impatrq/visiondrive/Cableado_Frenos_Luces/Cableado parte 1 vehiculo1.jpg

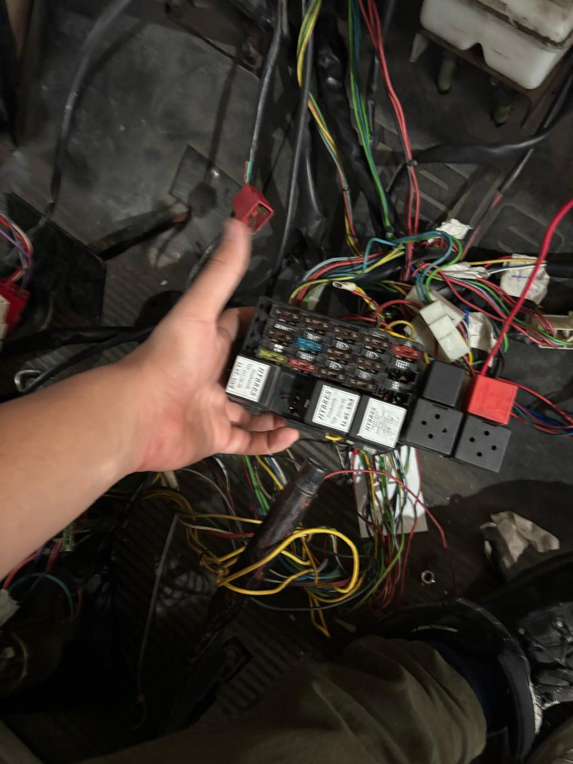
Cableado_Frenos_Luces/Cableado parte 1 vehiculo1.jpg
