impatrq/visiondrive/Cableado_Frenos_Luces/cableado parte 2 vehiculo 1.jpg

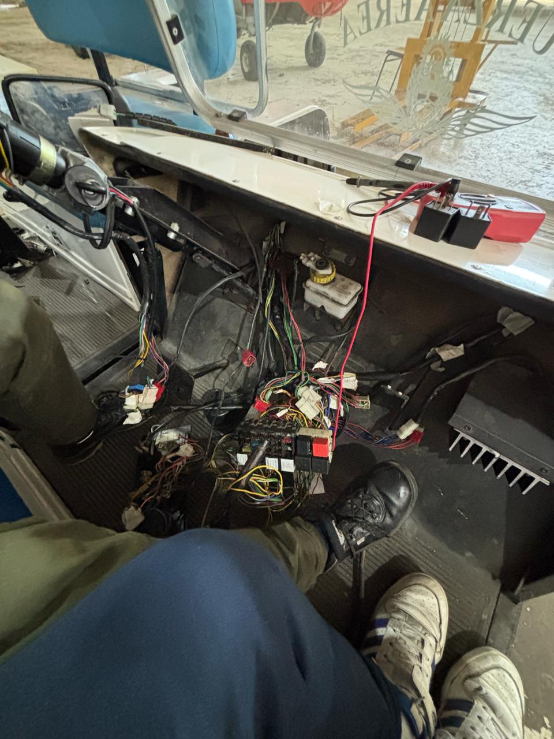
Cableado_Frenos_Luces/cableado parte 2 vehiculo 1.jpg
