impatrq/visiondrive/Carros Melex/Armado/Opticas/Imagen de WhatsApp 2024-11-14 a las 22.56.18_2eb6550c.jpg

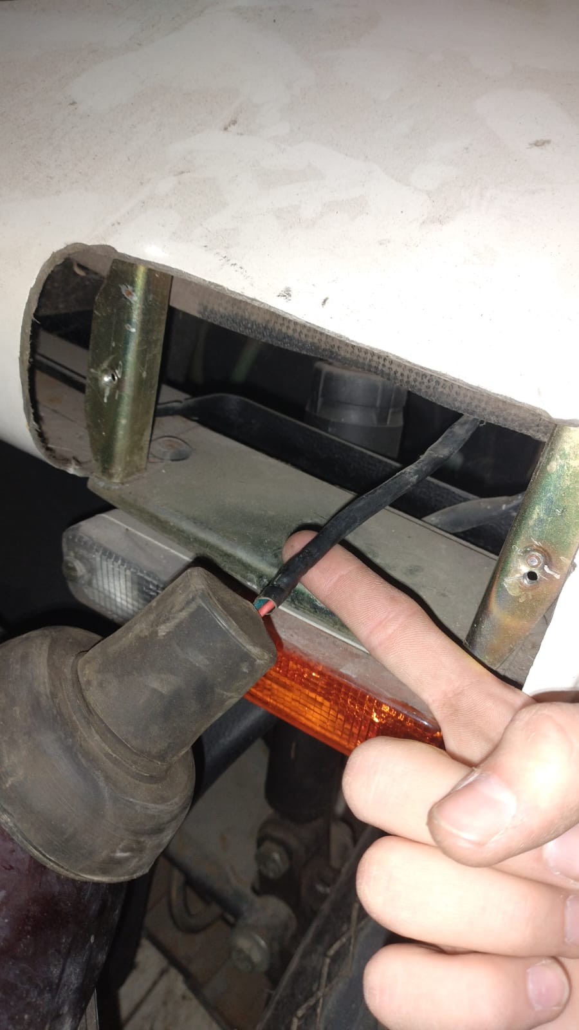
Carros Melex/Armado/Opticas/Imagen de WhatsApp 2024-11-14 a las 22.56.18_2eb6550c.jpg
