impatrq/visiondrive/Documentación/Diagramas de bloques/diagrama de bloques actualizado.png

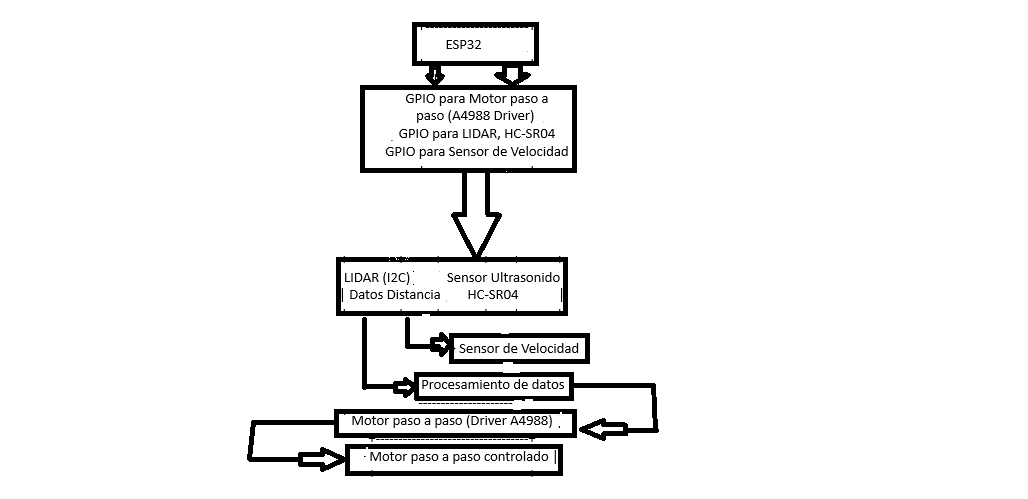
Documentación/Diagramas de bloques/diagrama de bloques actualizado.png
