impatrq/visiondrive/Documentación/Diagramas de bloques/diagrama de bloques.png

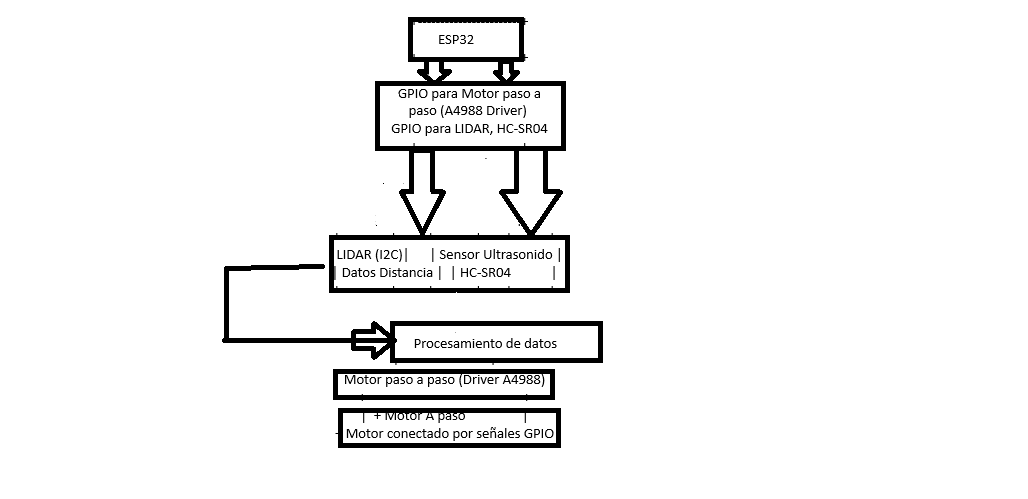
Documentación/Diagramas de bloques/diagrama de bloques.png
