impatrq/visiondrive/Impresiones 3D/Diseños de piezas 3d/diseño de segunda pieza 3d .jpg

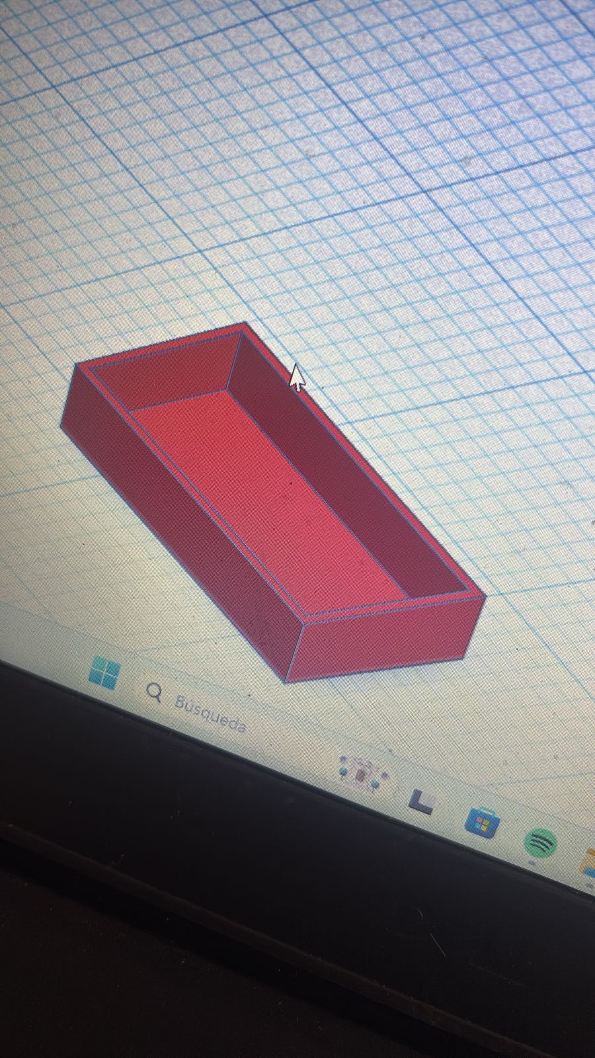
Impresiones 3D/Diseños de piezas 3d/diseño de segunda pieza 3d .jpg
