impatrq/visiondrive/Impresiones 3D/Piezas 3D/16E25E6C-24CF-4ABC-BED1-2C66113891F4.jpeg

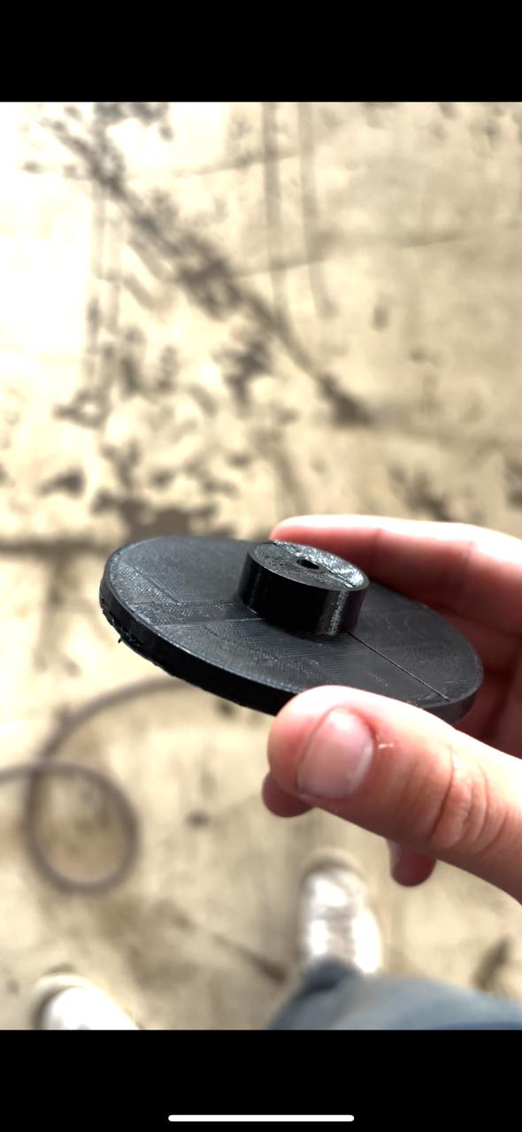
Impresiones 3D/Piezas 3D/16E25E6C-24CF-4ABC-BED1-2C66113891F4.jpeg
