impatrq/visiondrive/Impresiones 3D/Piezas 3D/265E03B3-B8B3-4103-B149-0D53786FD9E9_1_105_c.jpeg

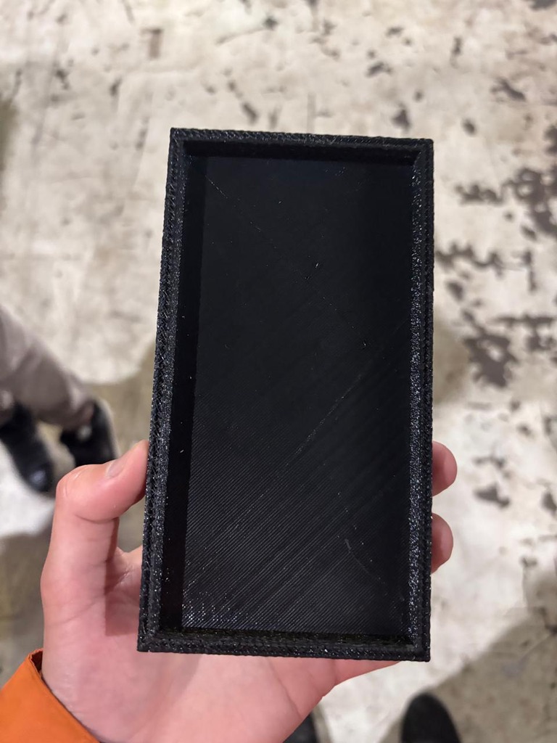
Impresiones 3D/Piezas 3D/265E03B3-B8B3-4103-B149-0D53786FD9E9_1_105_c.jpeg
