impatrq/visiondrive/mano de obra freno/20241107_143116.jpg

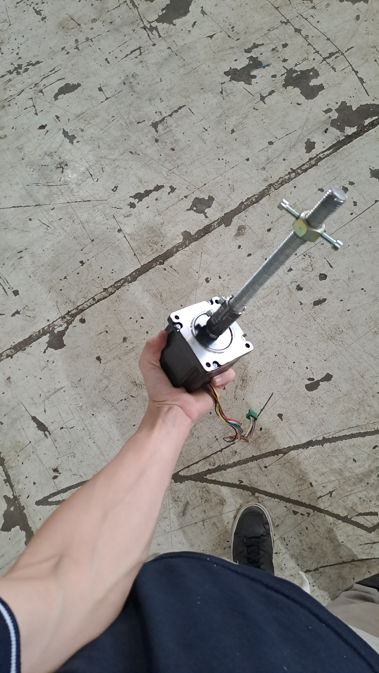
mano de obra freno/20241107_143116.jpg
