impatrq/visiondrive/mano de obra freno/20241107_165553.jpg

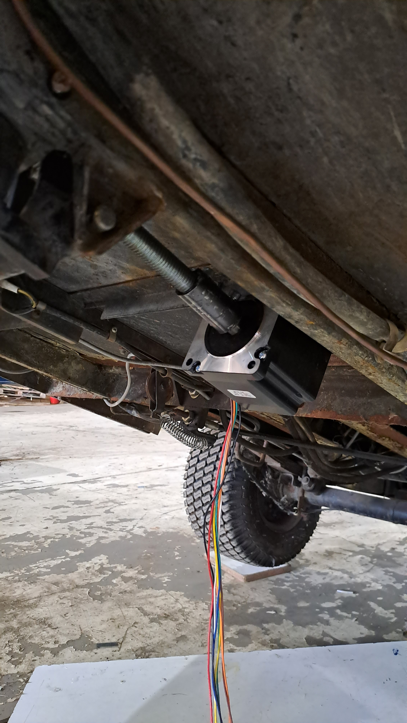
mano de obra freno/20241107_165553.jpg
