impatrq/visiondrive/mano de obra freno/20241107_165602.jpg

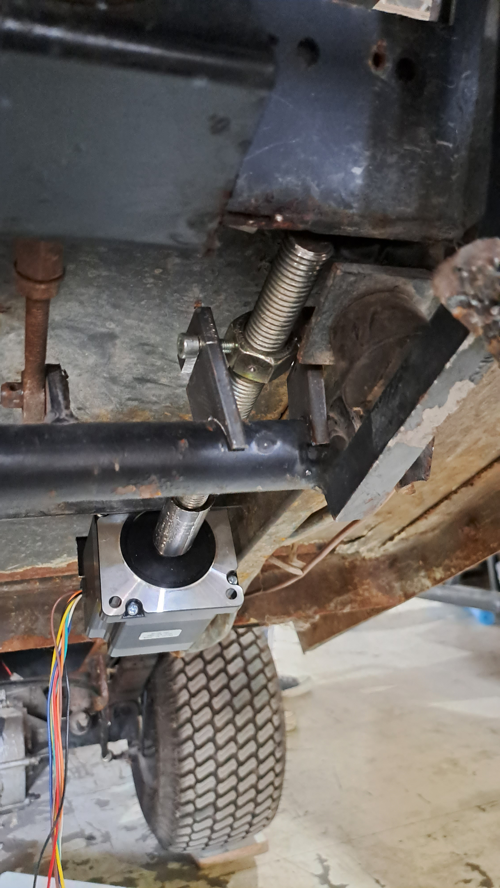
mano de obra freno/20241107_165602.jpg
