impatrq/visiondrive/mano de obra freno/20241107_165605.jpg

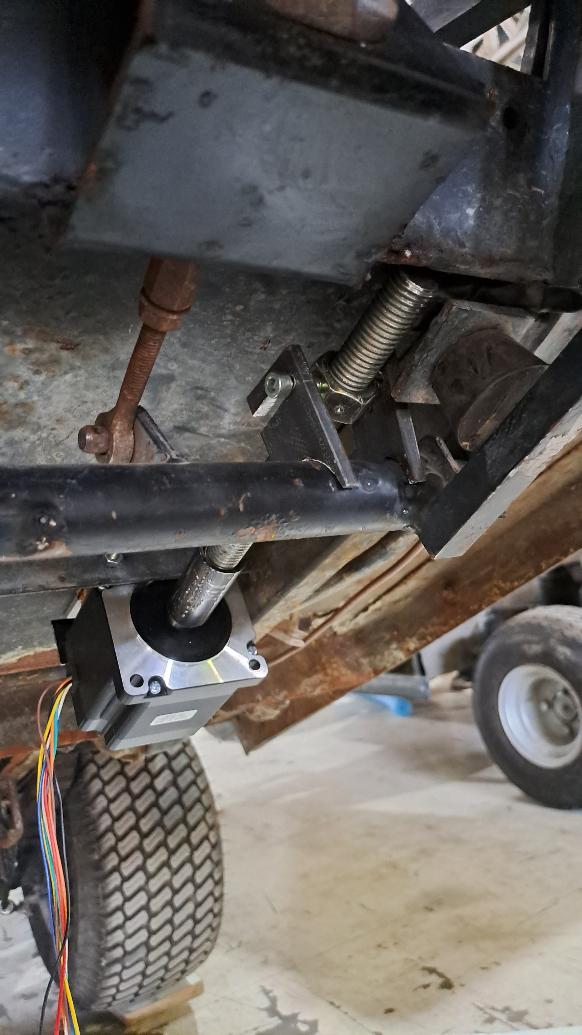
mano de obra freno/20241107_165605.jpg
