impatrq/visiondrive/mano de obra freno/Screenshot_20241029_111633_Video Player.jpg

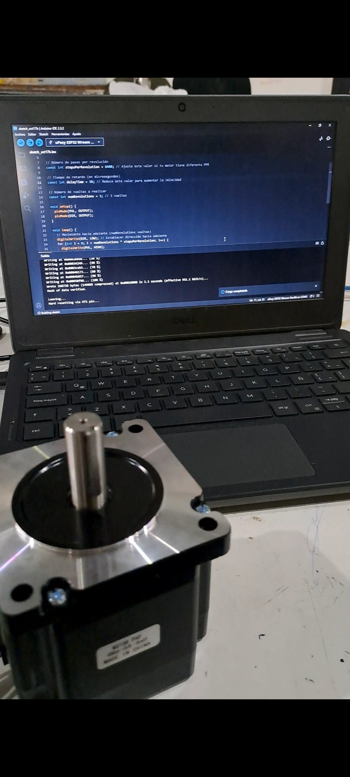
mano de obra freno/Screenshot_20241029_111633_Video Player.jpg
