impatrq/visiondrive/mano de obra freno/Screenshot_20241114_141442_WhatsApp.jpg

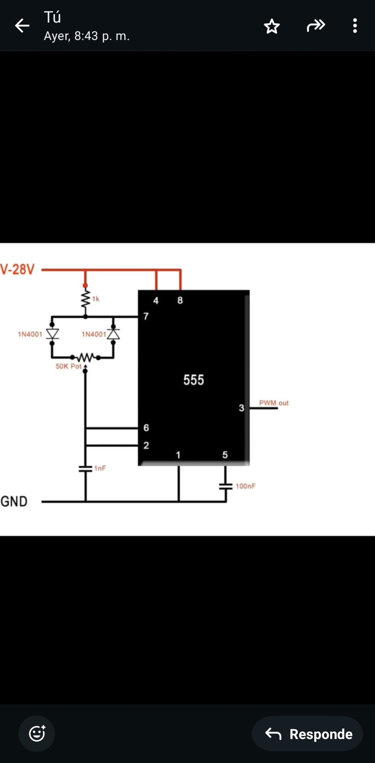
mano de obra freno/Screenshot_20241114_141442_WhatsApp.jpg
