impatrq/visiondrive/Pagina Web/Captura de pantalla 2024-11-15 085541.png

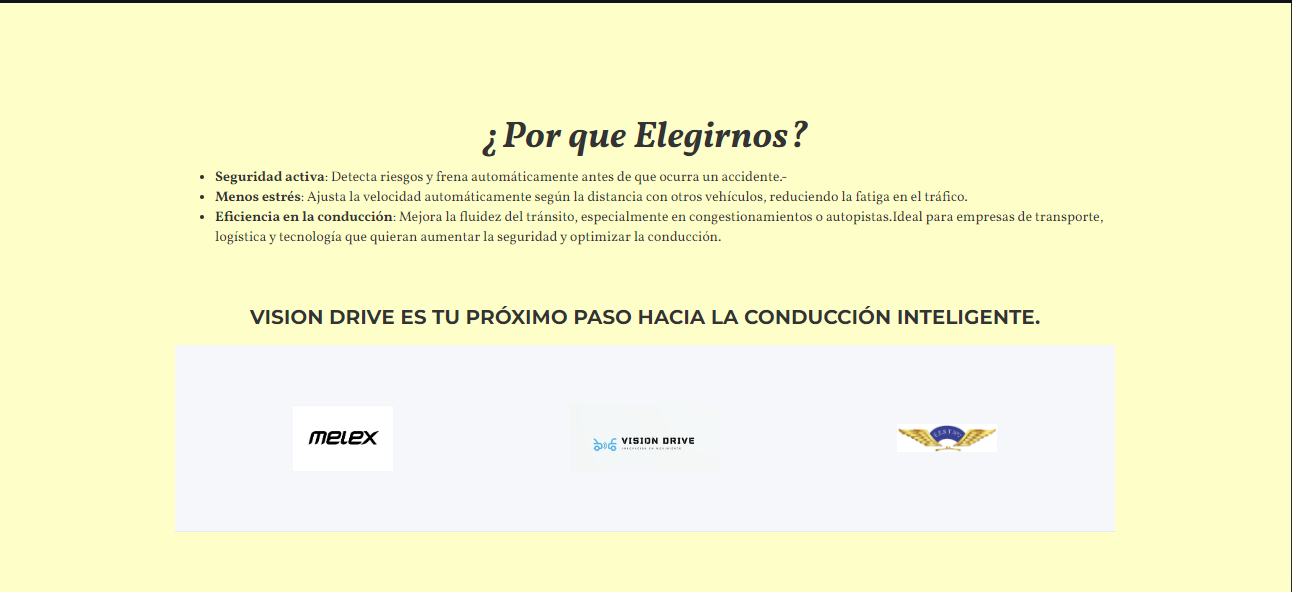
Pagina Web/Captura de pantalla 2024-11-15 085541.png
