impatrq/visiondrive/Pagina Web/Como Surge Esta idea Seccion.png

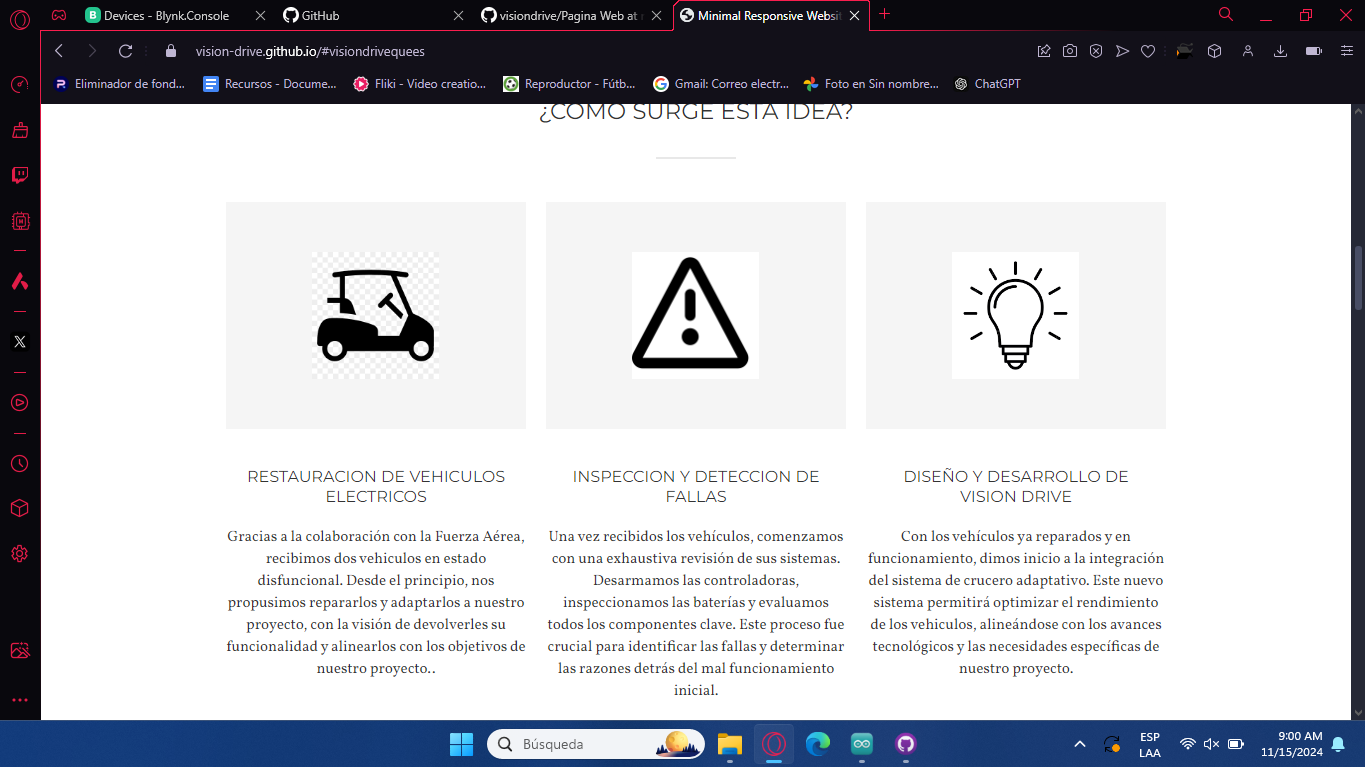
Pagina Web/Como Surge Esta idea Seccion.png
