impatrq/visiondrive/Pagina Web/Contacto Seccion.png

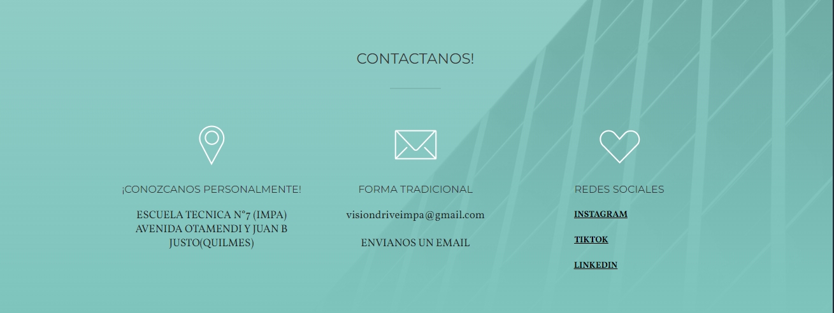
Pagina Web/Contacto Seccion.png
