impatrq/visiondrive/Pagina Web/Integrantes Seccion.png

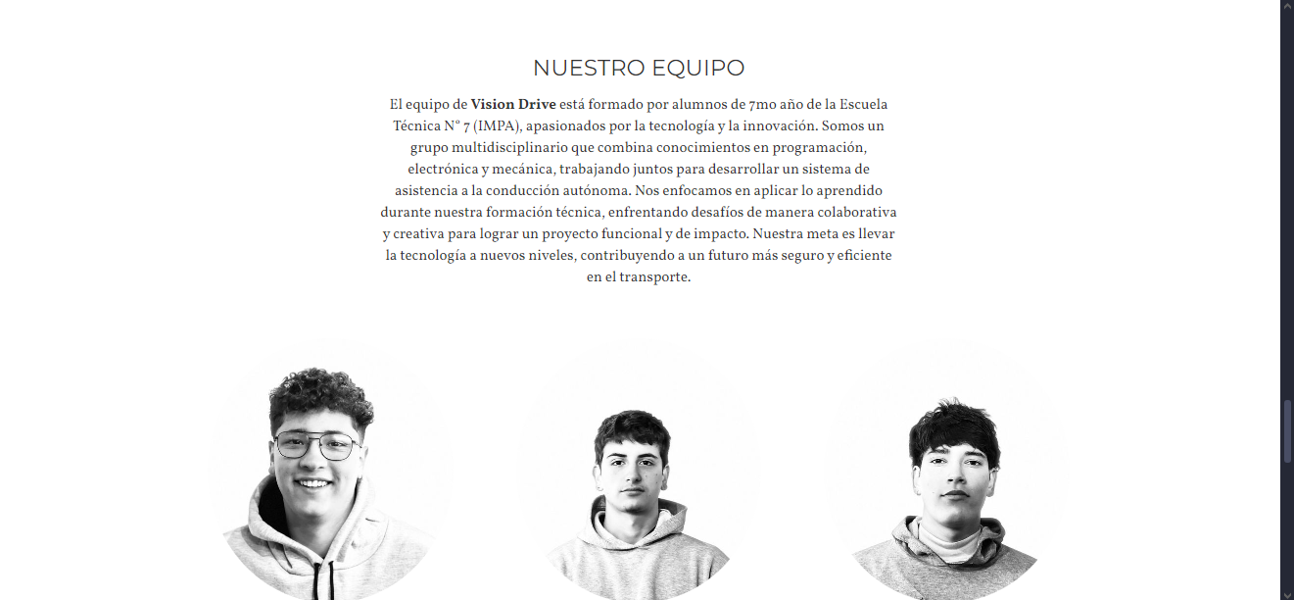
Pagina Web/Integrantes Seccion.png
