impatrq/visiondrive/Pagina Web/Proceso Parte 1.png

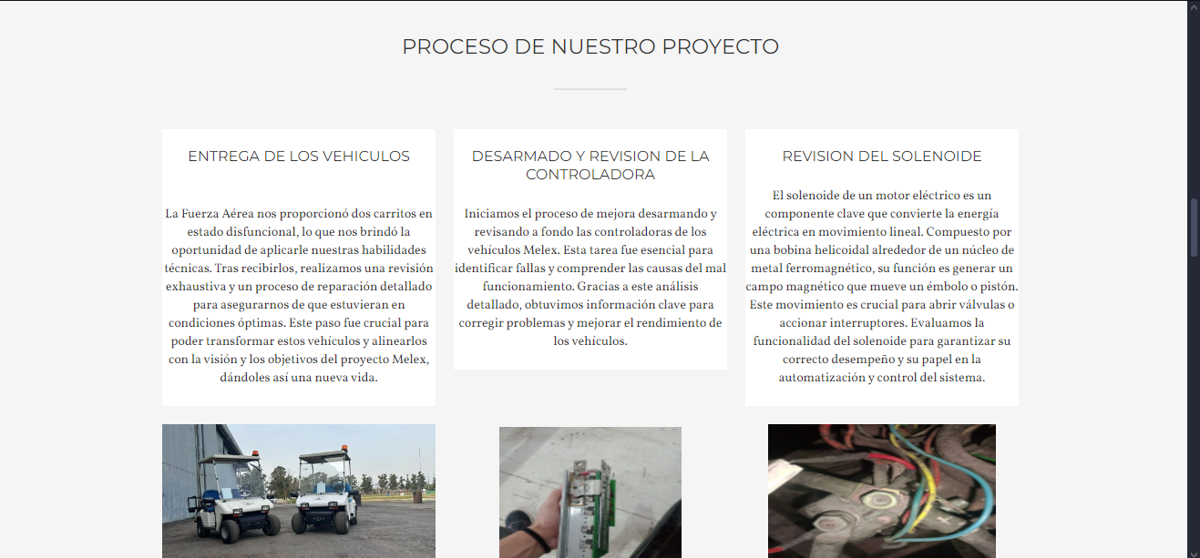
Pagina Web/Proceso Parte 1.png
