impatrq/visiondrive/Pagina Web/Proceso Parte 2.png

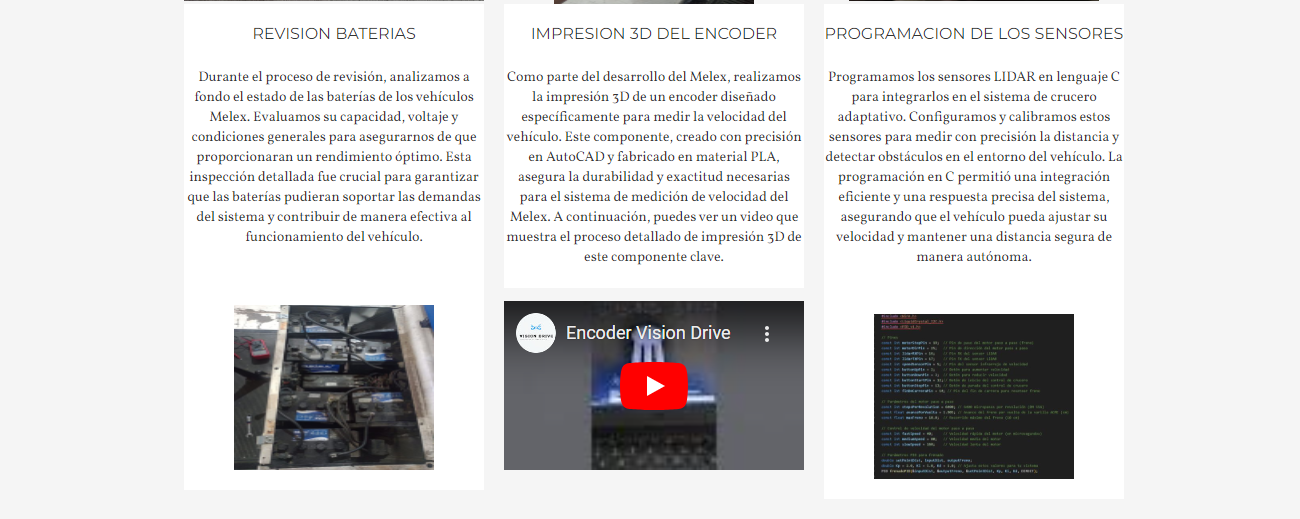
Pagina Web/Proceso Parte 2.png
