impatrq/visiondrive/Pagina Web/Proceso Parte 3.png

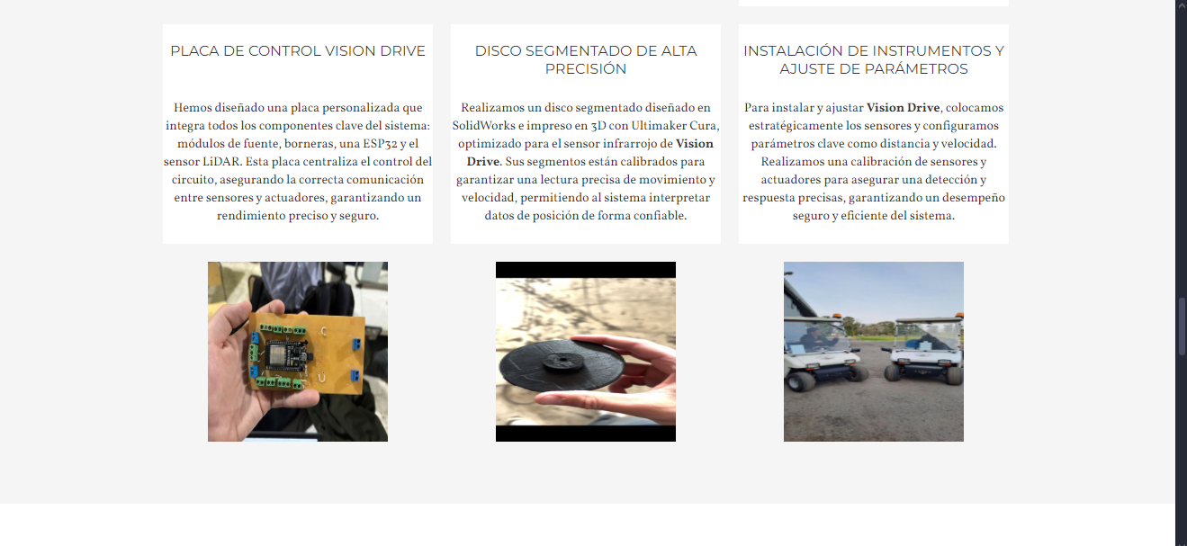
Pagina Web/Proceso Parte 3.png
