impatrq/visiondrive/Pagina Web/Seccion De inicio.png

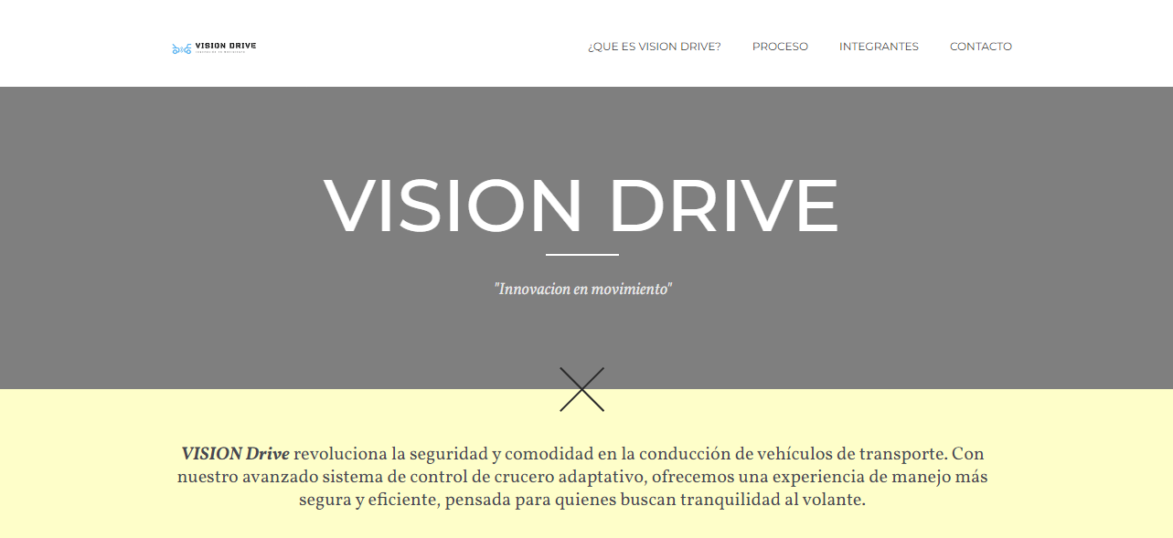
Pagina Web/Seccion De inicio.png
