impatrq/visiondrive/Placas del sistema/Placa madre/Esquematico/Captura de pantalla 2024-11-13 190311.png

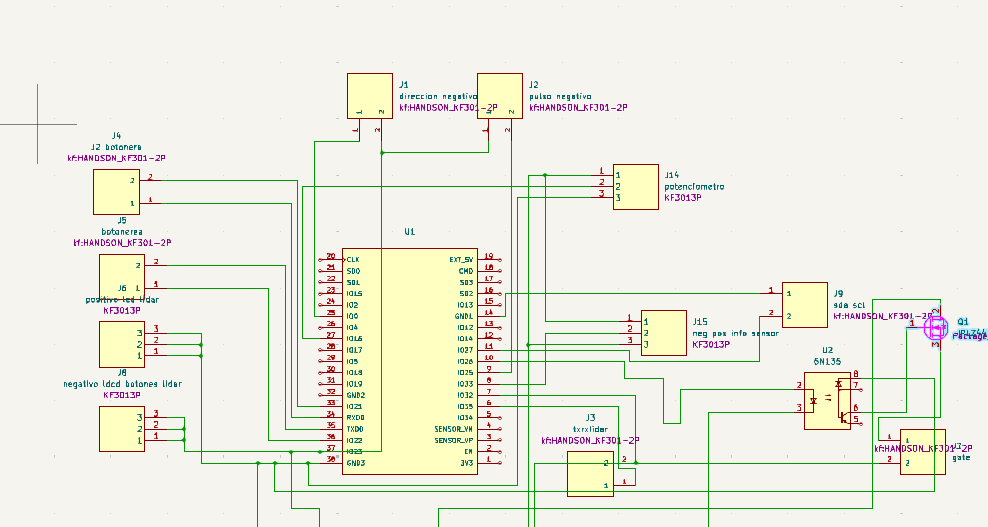
Placas del sistema/Placa madre/Esquematico/Captura de pantalla 2024-11-13 190311.png
