impatrq/visiondrive/Placas del sistema/Placa Madre/Esquematico/Captura de pantalla 2024-11-13 190333.png

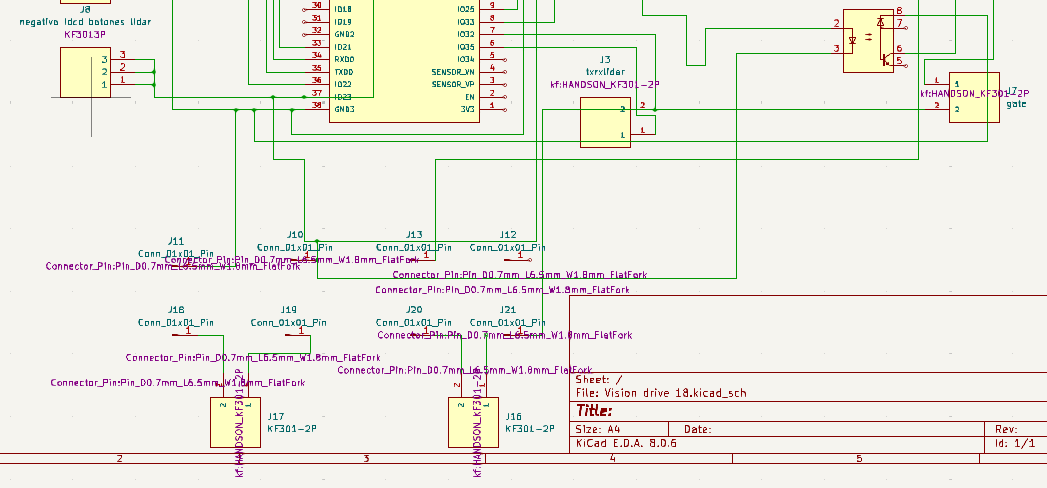
Placas del sistema/Placa Madre/Esquematico/Captura de pantalla 2024-11-13 190333.png
