impatrq/visiondrive/Placas del sistema/Placa Madre/Esquematico/Imagen de WhatsApp 2024-11-14 a las 22.43.56_5f30c6e0.jpg

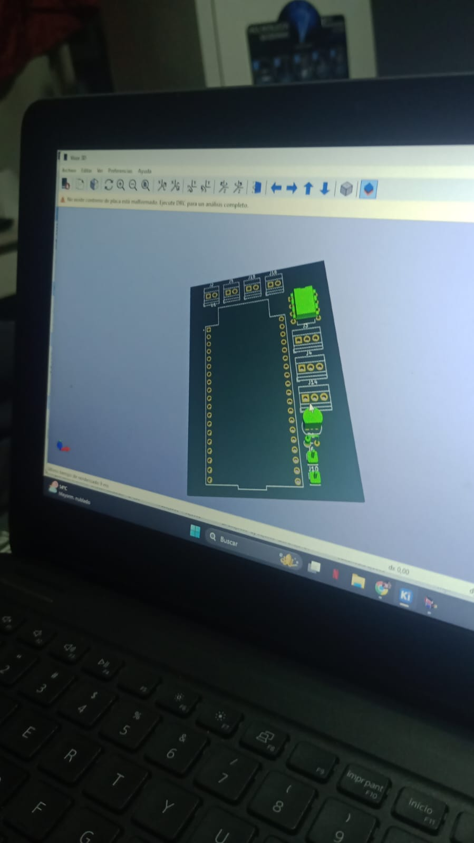
Placas del sistema/Placa Madre/Esquematico/Imagen de WhatsApp 2024-11-14 a las 22.43.56_5f30c6e0.jpg
