impatrq/visiondrive/Placas del sistema/Placa madre/Modelo 3D/Captura de pantalla 2024-11-16 204222.png

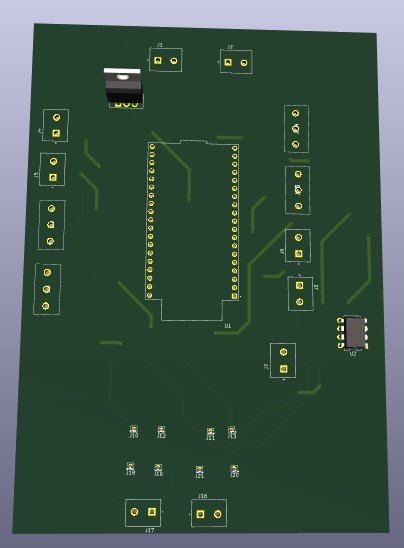
Placas del sistema/Placa madre/Modelo 3D/Captura de pantalla 2024-11-16 204222.png
