impatrq/visiondrive/Placas del sistema/Placa Madre/PCB/Captura de pantalla 2024-11-13 190235.png

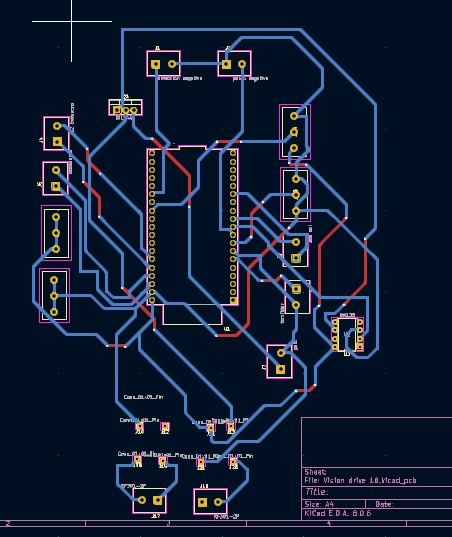
Placas del sistema/Placa Madre/PCB/Captura de pantalla 2024-11-13 190235.png
