impatrq/visiondrive/Placas del sistema/Placa Madre/Placa/Imagen de WhatsApp 2024-11-14 a las 21.38.06_84a4745a.jpg

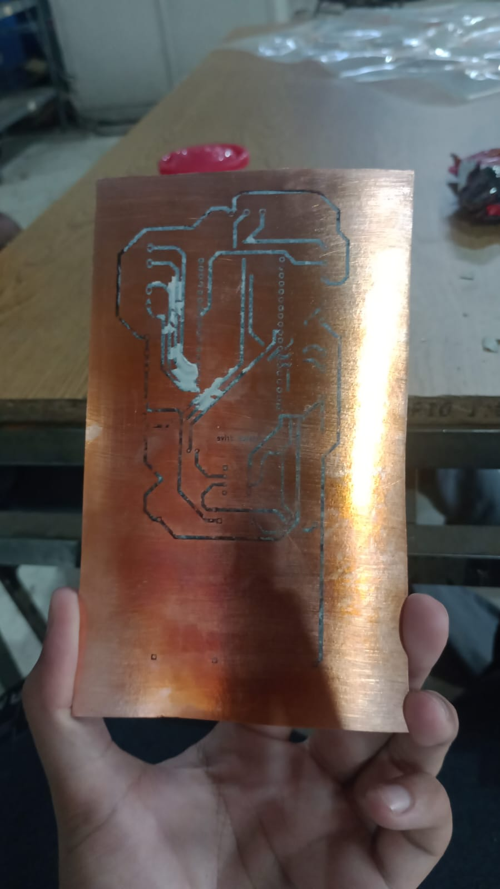
Placas del sistema/Placa Madre/Placa/Imagen de WhatsApp 2024-11-14 a las 21.38.06_84a4745a.jpg
