impatrq/visiondrive/Placas del sistema/Placa pwm/Esquematico/Captura de pantalla 2024-11-14 162236.png

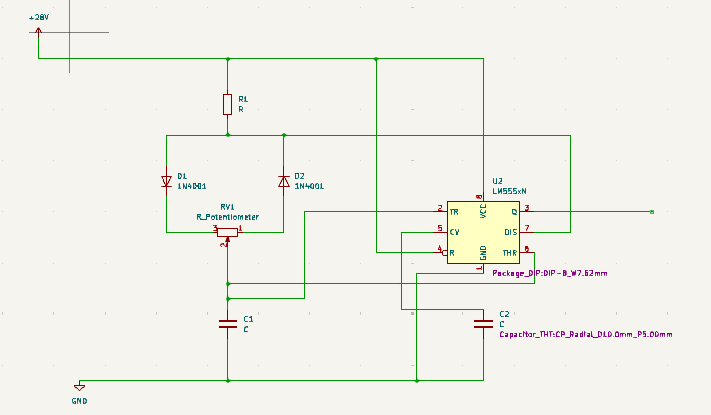
Placas del sistema/Placa pwm/Esquematico/Captura de pantalla 2024-11-14 162236.png
