impatrq/visiondrive/Placas del sistema/Placa pwm/Esquematico/Captura de pantalla 2024-11-16 133115.png

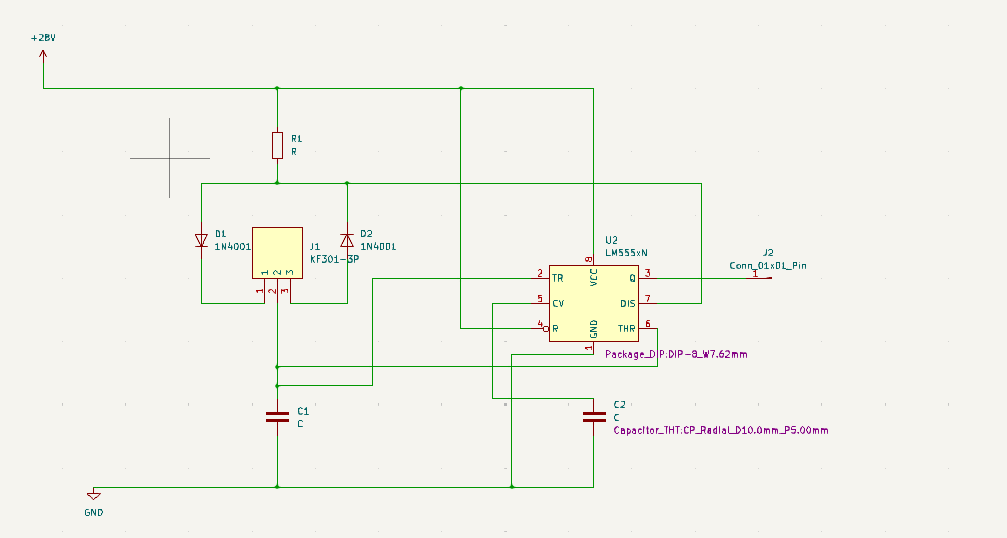
Placas del sistema/Placa pwm/Esquematico/Captura de pantalla 2024-11-16 133115.png
