impatrq/visiondrive/Placas del sistema/Placa pwm/Modelo 3D/Captura de pantalla 2024-11-16 205208.png

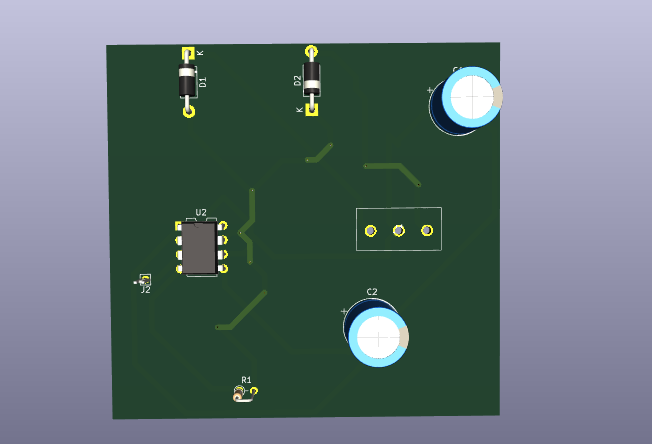
Placas del sistema/Placa pwm/Modelo 3D/Captura de pantalla 2024-11-16 205208.png
