impatrq/visiondrive/Placas del sistema/Placa pwm/PCB/Captura de pantalla 2024-11-14 115834.png

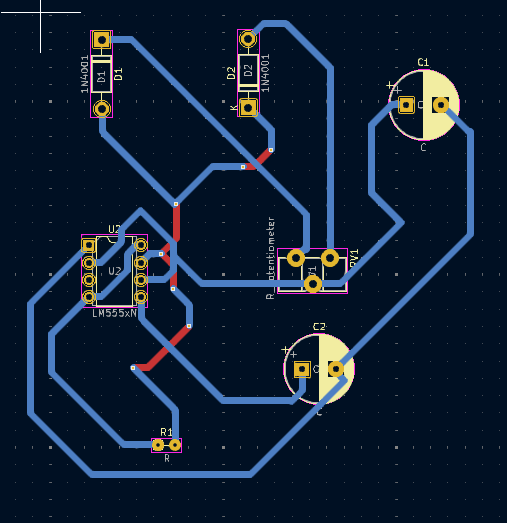
Placas del sistema/Placa pwm/PCB/Captura de pantalla 2024-11-14 115834.png
