impatrq/visiondrive/Placas del sistema/Placa pwm/PCB/Captura de pantalla 2024-11-16 133915.png

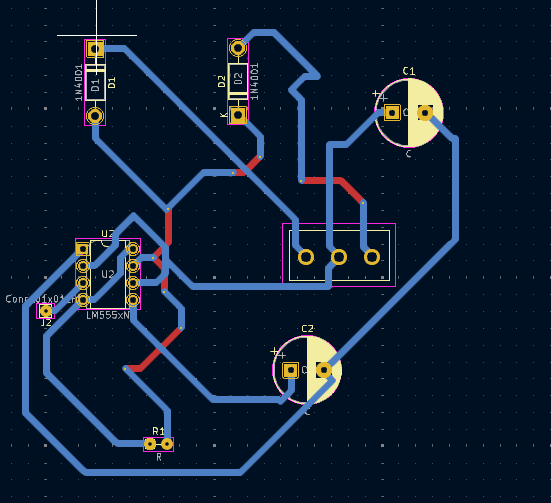
Placas del sistema/Placa pwm/PCB/Captura de pantalla 2024-11-16 133915.png
