impatrq/visiondrive/Redes Sociales/Instagram/Historias/HistoriaMiembros.jpeg

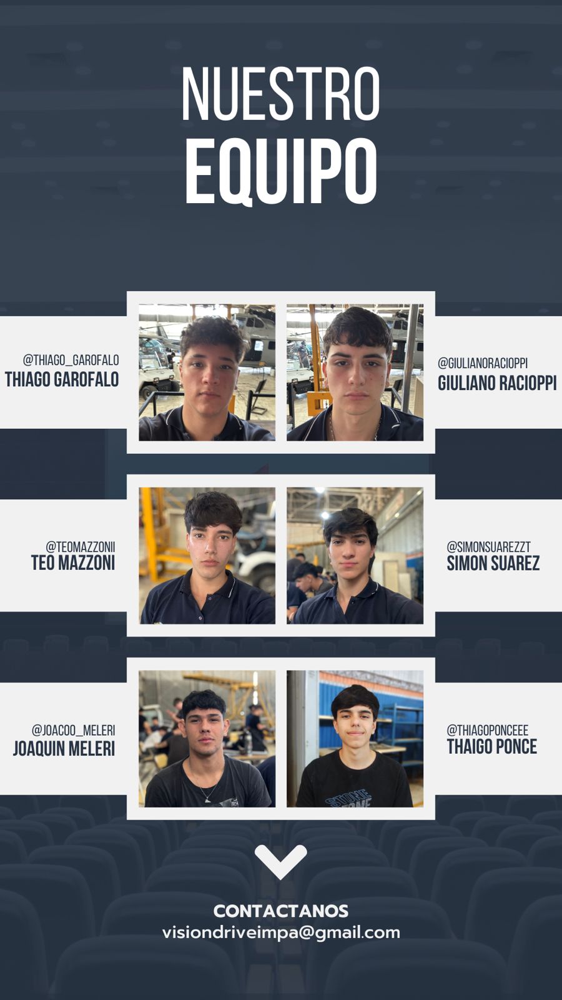
Redes Sociales/Instagram/Historias/HistoriaMiembros.jpeg
