impatrq/visiondrive/Carros Melex/Armado/Armado motor Paso a Paso/trello1104647121019756296.jpg

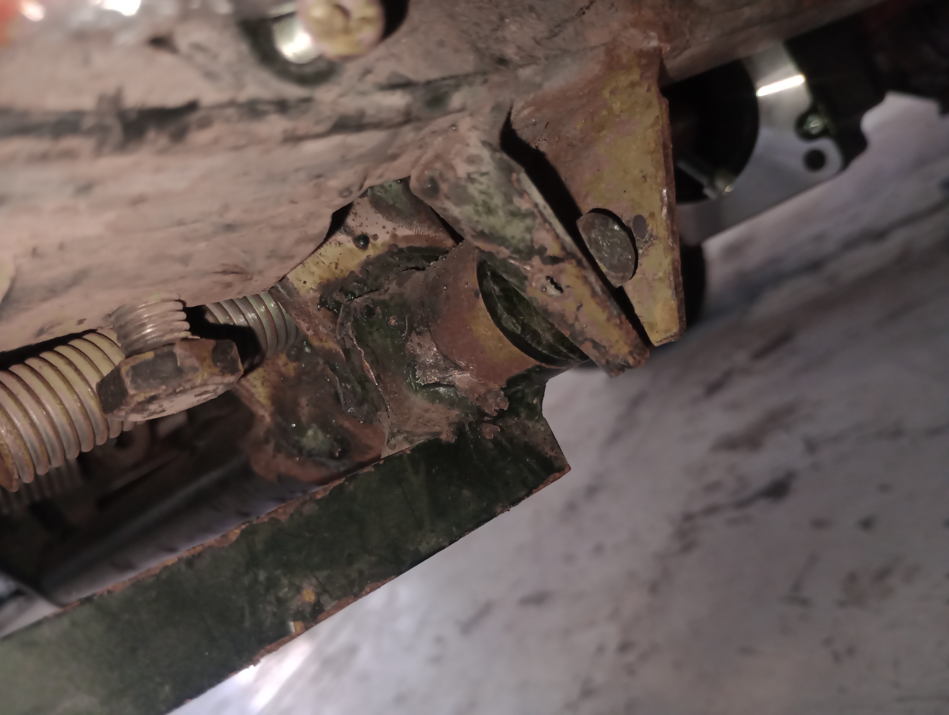
Carros Melex/Armado/Armado motor Paso a Paso/trello1104647121019756296.jpg
