impatrq/visiondrive/Carros Melex/Armado/Baterias/Baterias.jpg

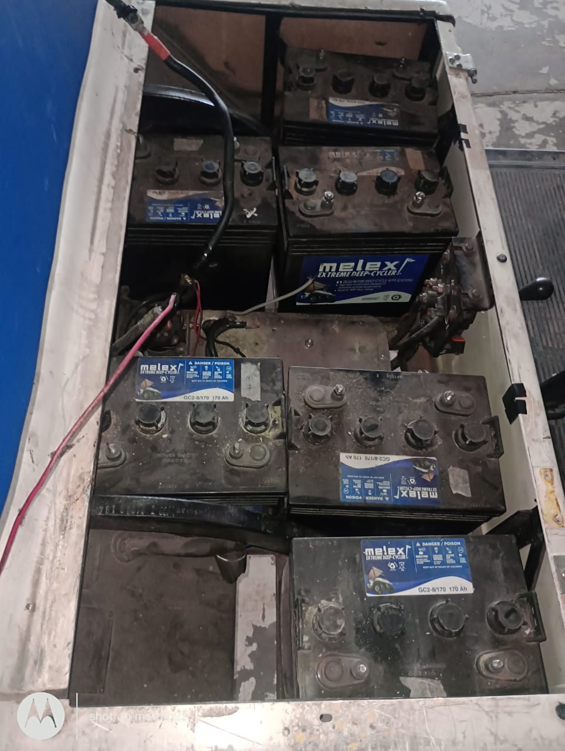
Carros Melex/Armado/Baterias/Baterias.jpg
