impatrq/visiondrive/Carros Melex/Armado/Cableado de luces/Imagen de WhatsApp 2024-11-14 a las 22.21.11_99121e55.jpg

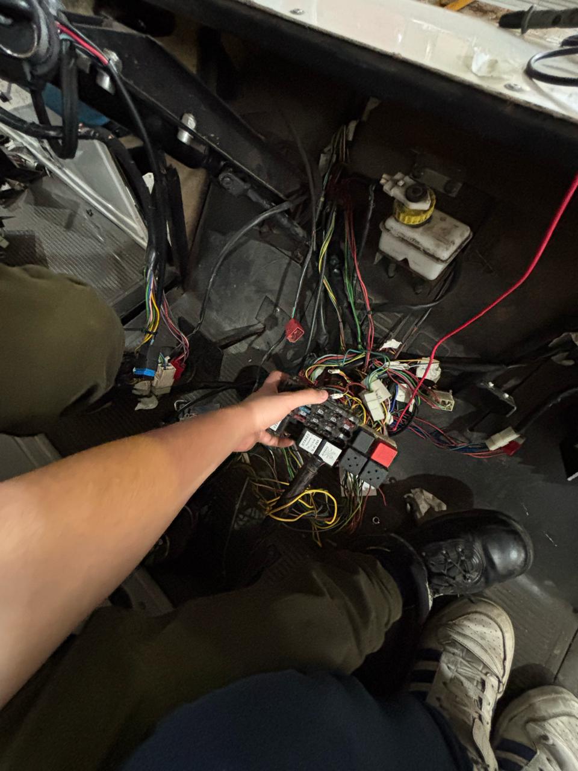
Carros Melex/Armado/Cableado de luces/Imagen de WhatsApp 2024-11-14 a las 22.21.11_99121e55.jpg
