impatrq/visiondrive/Carros Melex/Armado/Cableado de luces/Imagen de WhatsApp 2024-11-14 a las 22.43.56_6ac86141.jpg

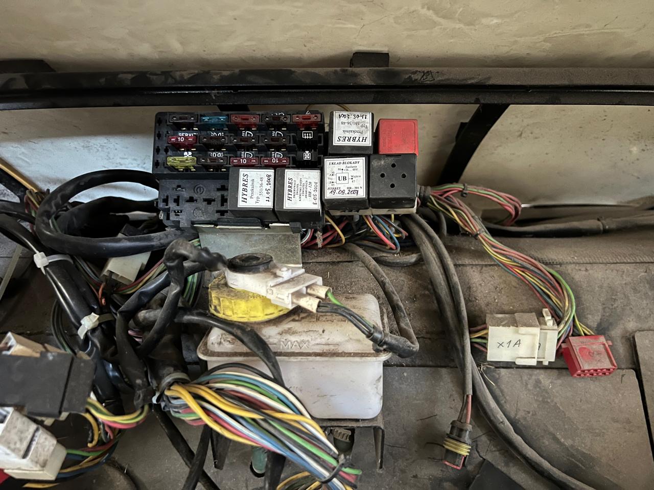
Carros Melex/Armado/Cableado de luces/Imagen de WhatsApp 2024-11-14 a las 22.43.56_6ac86141.jpg
