impatrq/visiondrive/Carros Melex/Armado/Colocacion disco segmentado/Colocacion disco segmentado 1.JPG

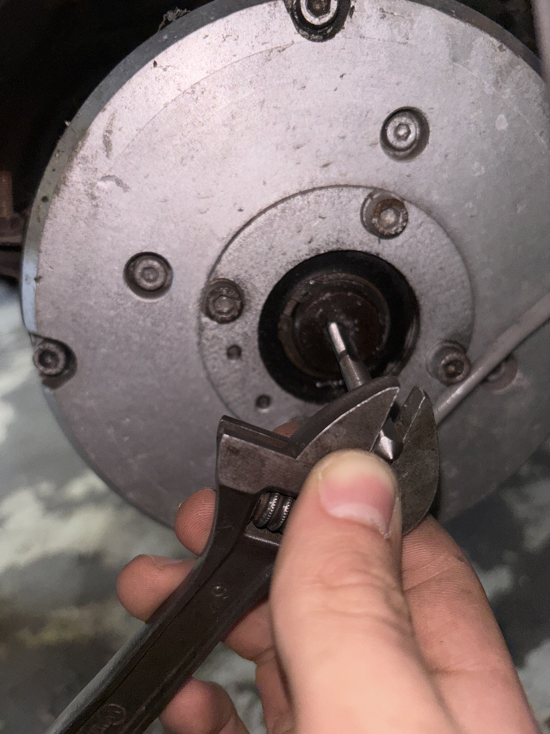
Carros Melex/Armado/Colocacion disco segmentado/Colocacion disco segmentado 1.JPG
