impatrq/visiondrive/Carros Melex/Armado/Controladora/controladora .jpg

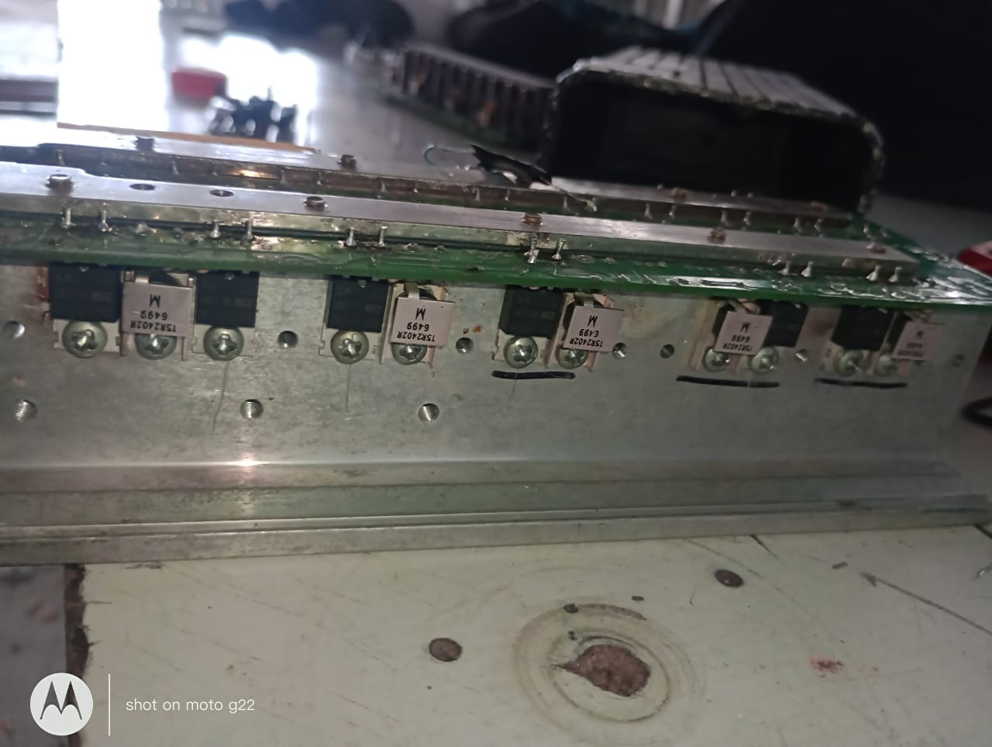
Carros Melex/Armado/Controladora/controladora .jpg
