impatrq/visiondrive/Carros Melex/Armado/Controladora/Controladora y PWM.jpg

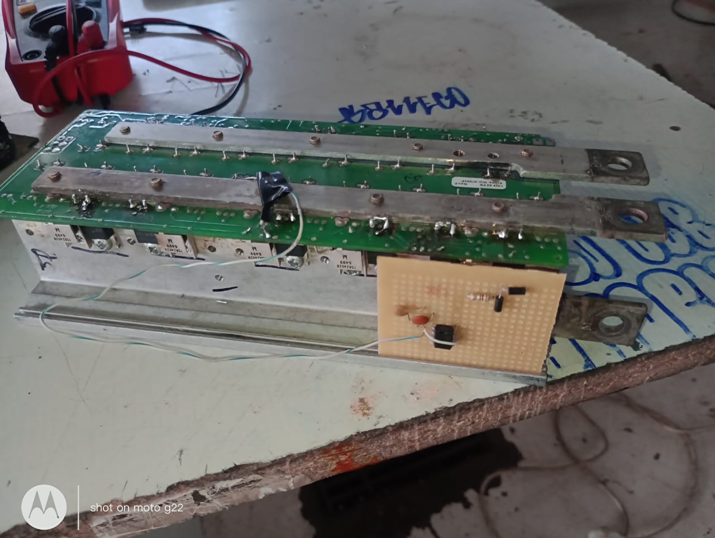
Carros Melex/Armado/Controladora/Controladora y PWM.jpg
