impatrq/visiondrive/Carros Melex/Armado/Controladora/Imagen de WhatsApp 2024-11-14 a las 22.56.11_4301f85c.jpg

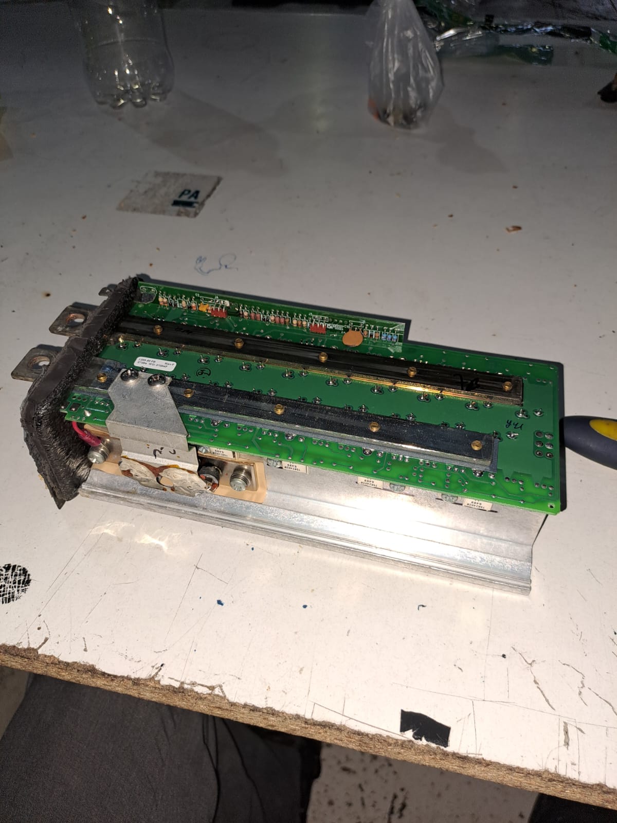
Carros Melex/Armado/Controladora/Imagen de WhatsApp 2024-11-14 a las 22.56.11_4301f85c.jpg
