impatrq/visiondrive/Carros Melex/Armado/Controladora/Imagen de WhatsApp 2024-11-14 a las 22.56.12_521d5b66.jpg

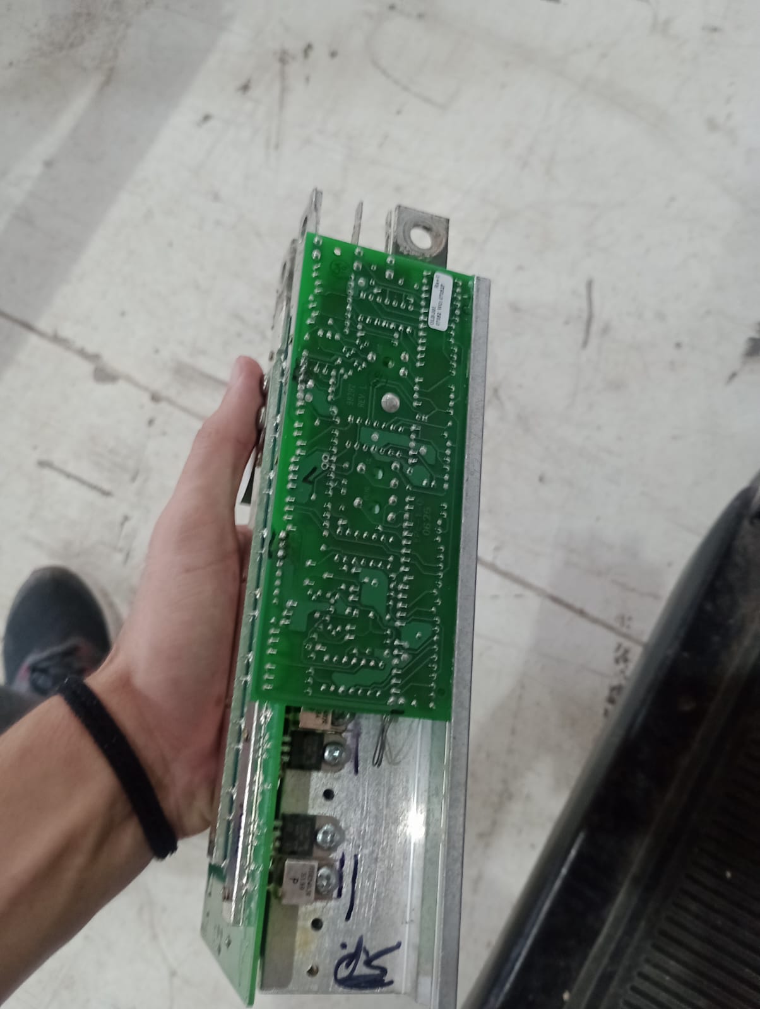
Carros Melex/Armado/Controladora/Imagen de WhatsApp 2024-11-14 a las 22.56.12_521d5b66.jpg
