impatrq/visiondrive/Carros Melex/Armado/Controladora/Imagen de WhatsApp 2024-12-14 a las 15.58.14_3410bcf5.jpg

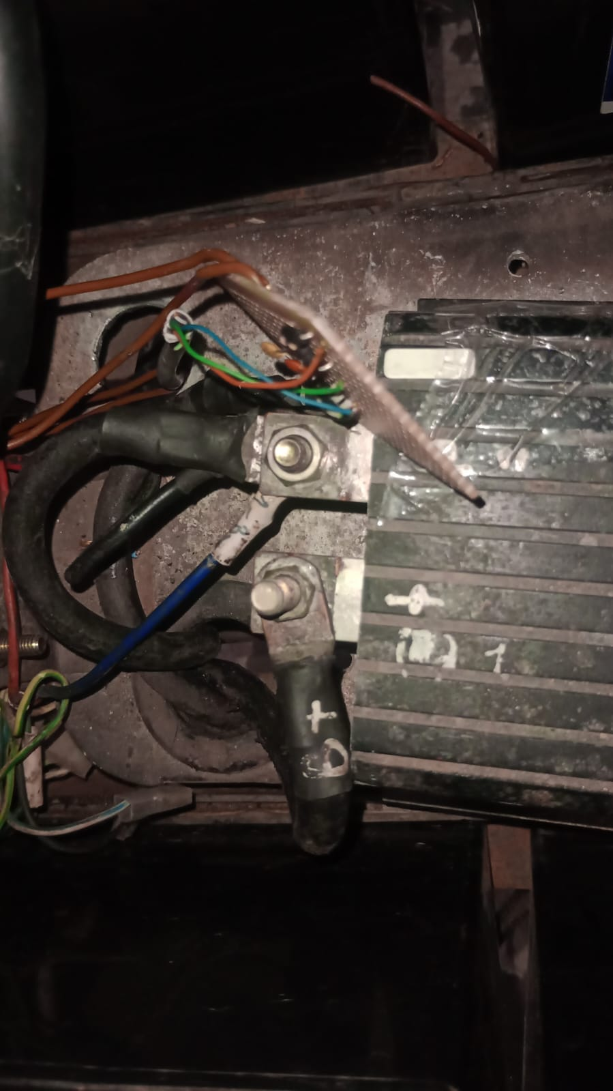
Carros Melex/Armado/Controladora/Imagen de WhatsApp 2024-12-14 a las 15.58.14_3410bcf5.jpg
