impatrq/visiondrive/Carros Melex/Armado/Controladora/Imagen de WhatsApp 2024-12-14 a las 15.58.15_9d04511b.jpg

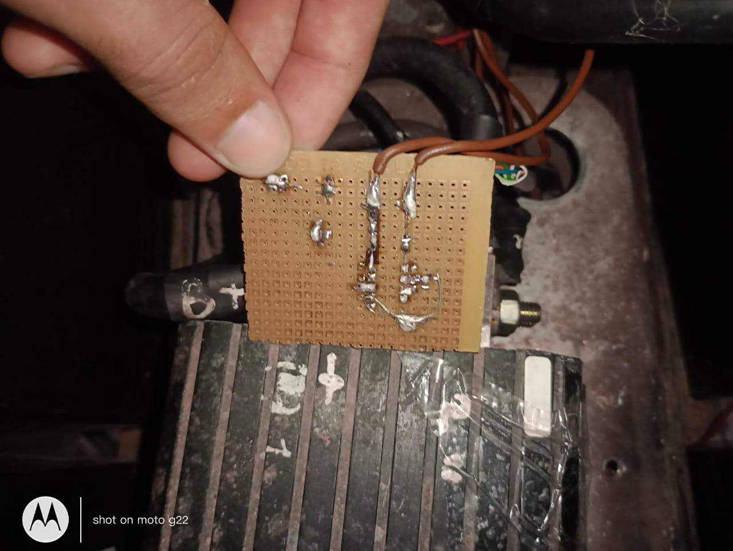
Carros Melex/Armado/Controladora/Imagen de WhatsApp 2024-12-14 a las 15.58.15_9d04511b.jpg
