impatrq/visiondrive/Carros Melex/Armado/Datos Motor Carrito/motor carrito melex.jpg

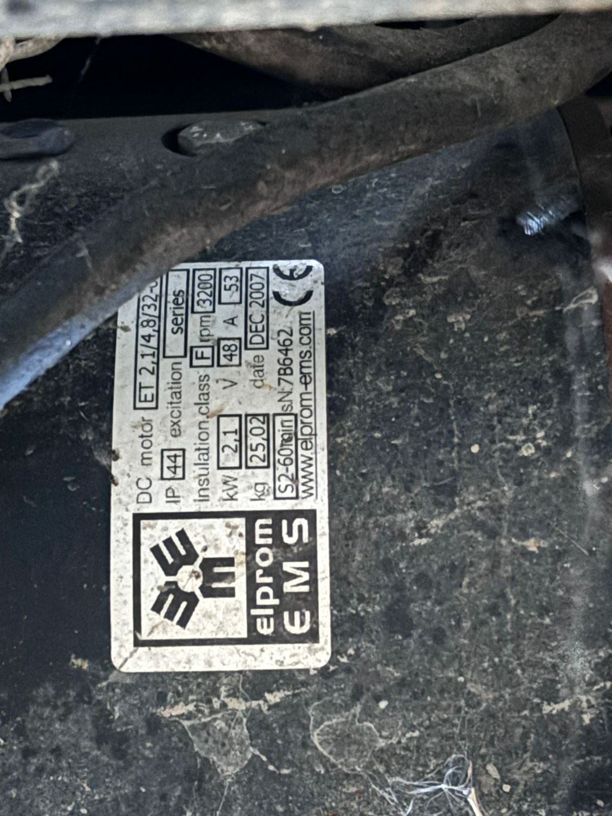
Carros Melex/Armado/Datos Motor Carrito/motor carrito melex.jpg
