impatrq/visiondrive/Carros Melex/Armado/Purgado de frenos/20240508_164337-1 (1).jpg

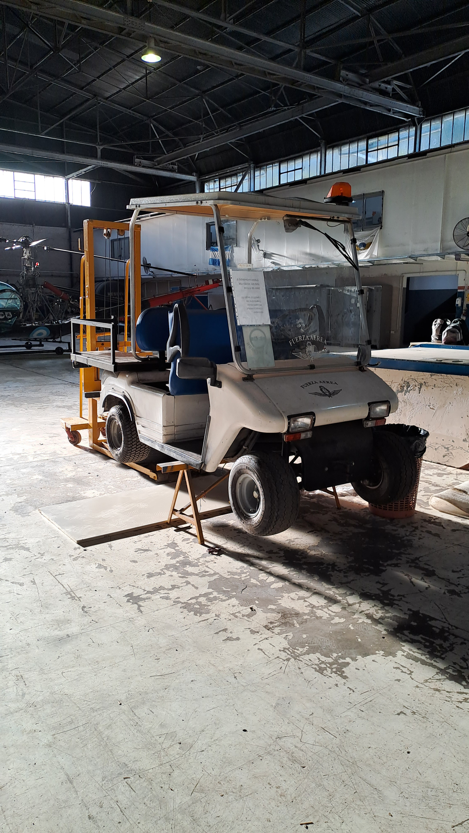
Carros Melex/Armado/Purgado de frenos/20240508_164337-1 (1).jpg
