impatrq/visiondrive/Carros Melex/Armado/PWM/pwm.jpg

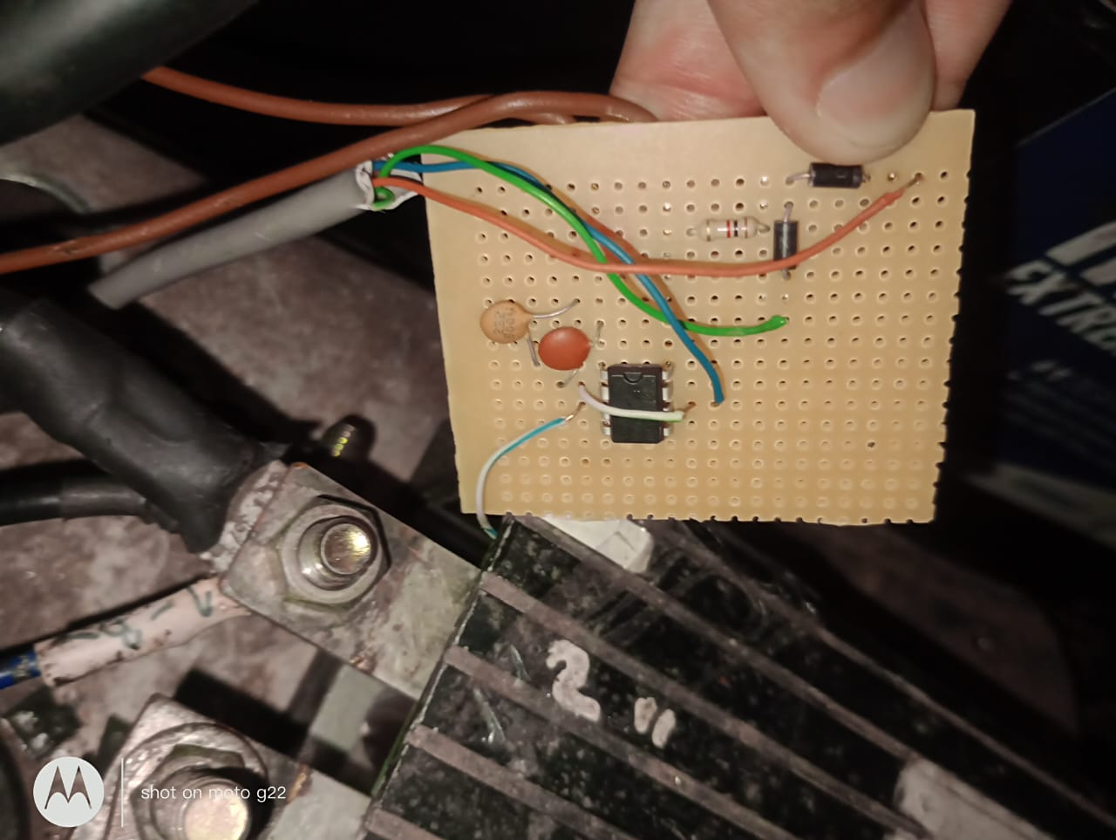
Carros Melex/Armado/PWM/pwm.jpg
