impatrq/visiondrive/Carros Melex/Armado/Solenoide/Imagen de WhatsApp 2024-11-14 a las 22.56.11_0ae3fb65.jpg

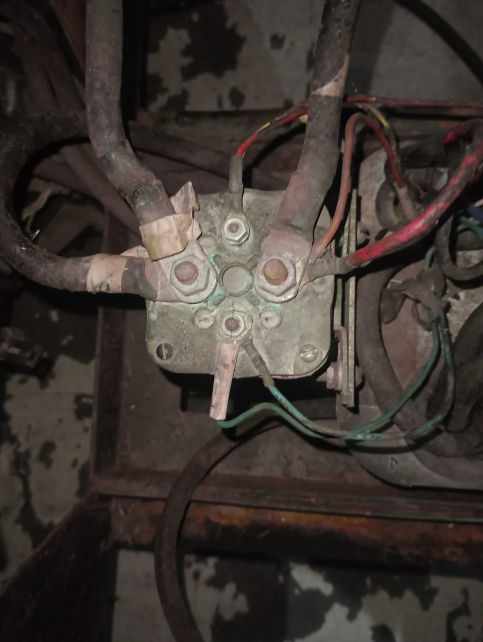
Carros Melex/Armado/Solenoide/Imagen de WhatsApp 2024-11-14 a las 22.56.11_0ae3fb65.jpg
