impatrq/visiondrive/Carros Melex/Armado/Solenoide/Imagen de WhatsApp 2024-12-14 a las 15.58.16_7fd8d137.jpg

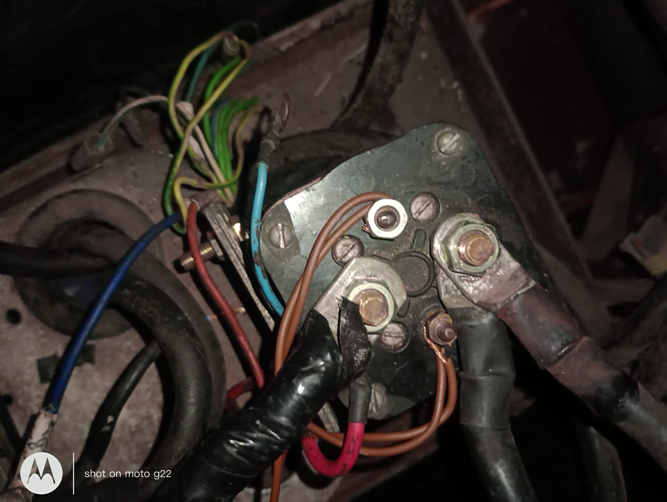
Carros Melex/Armado/Solenoide/Imagen de WhatsApp 2024-12-14 a las 15.58.16_7fd8d137.jpg
