impatrq/visiondrive/Carros Melex/Armado/tablero de luces/Imagen de WhatsApp 2024-11-15 a las 22.40.53_7b77b698.jpg

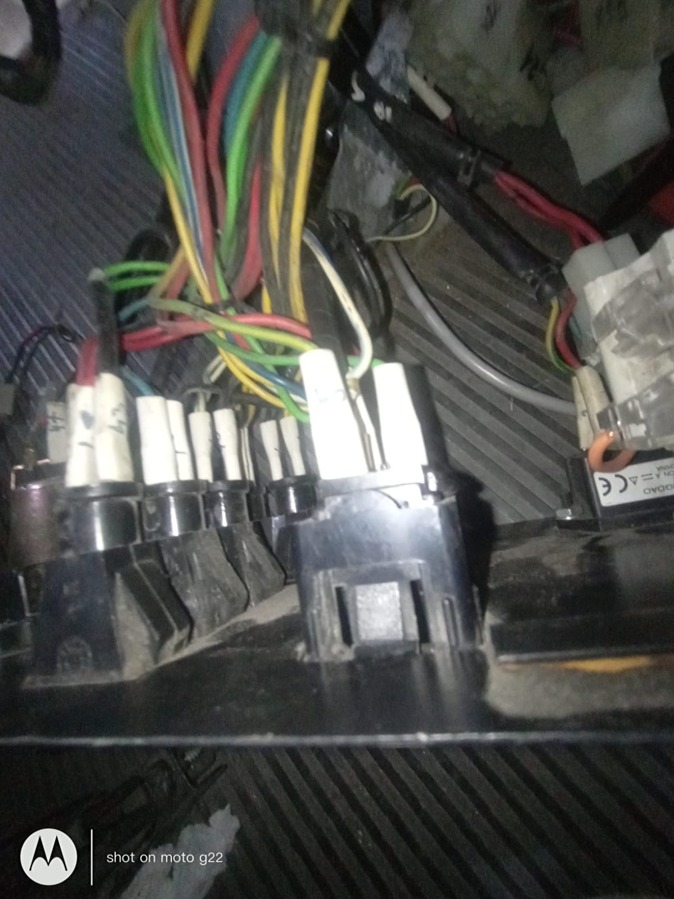
Carros Melex/Armado/tablero de luces/Imagen de WhatsApp 2024-11-15 a las 22.40.53_7b77b698.jpg
