impatrq/visiondrive/Carros Melex/Armado/tablero de luces/IMG_20241202_104126156 (3).jpg

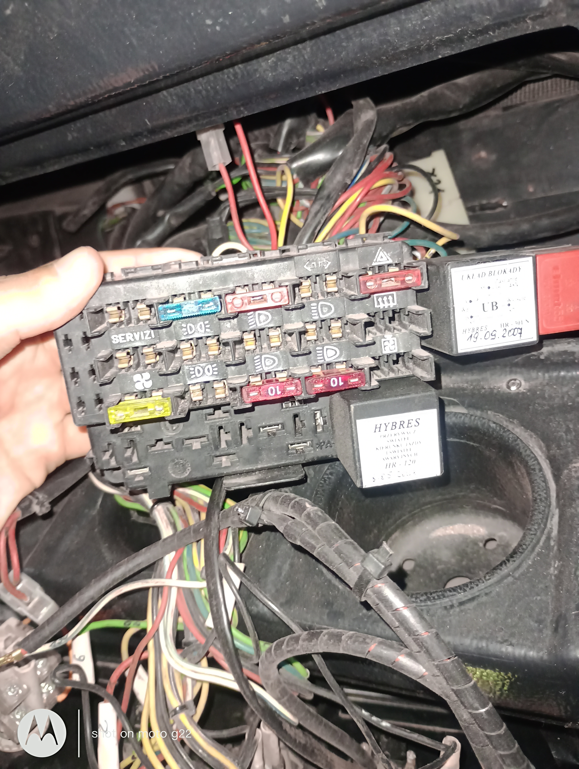
Carros Melex/Armado/tablero de luces/IMG_20241202_104126156 (3).jpg
