impatrq/visiondrive/Pruebas Con los Vehiculos/Prueba con ambos MELEX.jpg

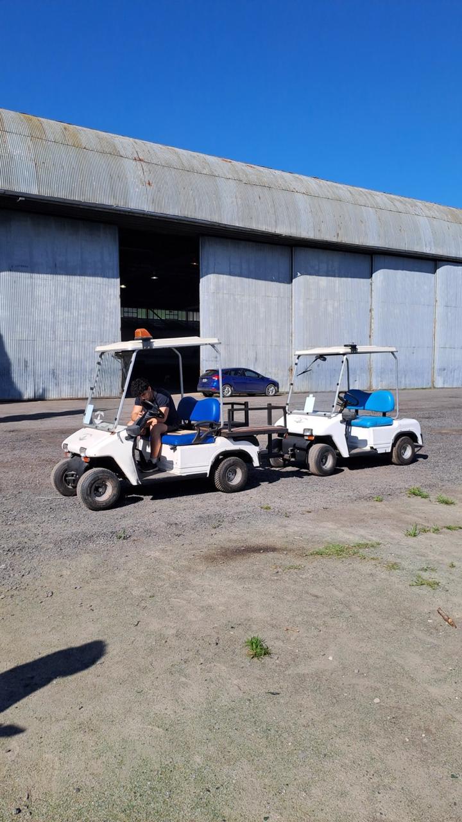
Pruebas Con los Vehiculos/Prueba con ambos MELEX.jpg
