impatrq/visiondrive/Codigo/primeros pasos interfaz/1codigointerfaz/1codigointerfaz.ino

#include <Arduino.h>
#include <Wire.h>
#include <LiquidCrystal_I2C.h> // Para la pantalla LCD

// Pines GPIO
const int lidarPin = 2;
const int speedSensorPin = 3;
const int brakeMotorPin = 4;
const int acceleratorMotorPin = 5;
const int potentiometerPin = 6;

// Objeto para la pantalla LCD
LiquidCrystal_I2C lcd(0x27, 16, 2);

// Variables para almacenar datos
float distance;
float currentSpeed;
float desiredSpeed;

// ... (código para inicializar los sensores, actuadores y la pantalla LCD)

void setup() {
  // ... (inicialización del ESP32)

  // Inicializar la pantalla LCD
  lcd.init();
  lcd.backlight();
}

void loop() {
  // Leer datos de los sensores
  distance = readLidarDistance(lidarPin);
  currentSpeed = readSpeedSensor(speedSensorPin);

  // Implementar el algoritmo de control de crucero
  desiredSpeed = getDesiredSpeed(potentiometerPin); 
  controlCruise(distance, currentSpeed, desiredSpeed);

  // Mostrar información en la pantalla LCD
  lcd.setCursor(0, 0);
  lcd.print("Velocidad: ");
  lcd.print(currentSpeed);

  lcd.setCursor(0, 1);
  lcd.print("Distancia: ");
  lcd.print(distance);

  // ... (gestionar las entradas de los botones)
}

// ... (funciones para leer los sensores, controlar el motor de freno, 
// controlar la velocidad del motor de aceleración, etc.)
