impatrq/visiondrive/Carros Melex/Armado/Colocacion disco segmentado/Colocacion disco segmentado2.JPG

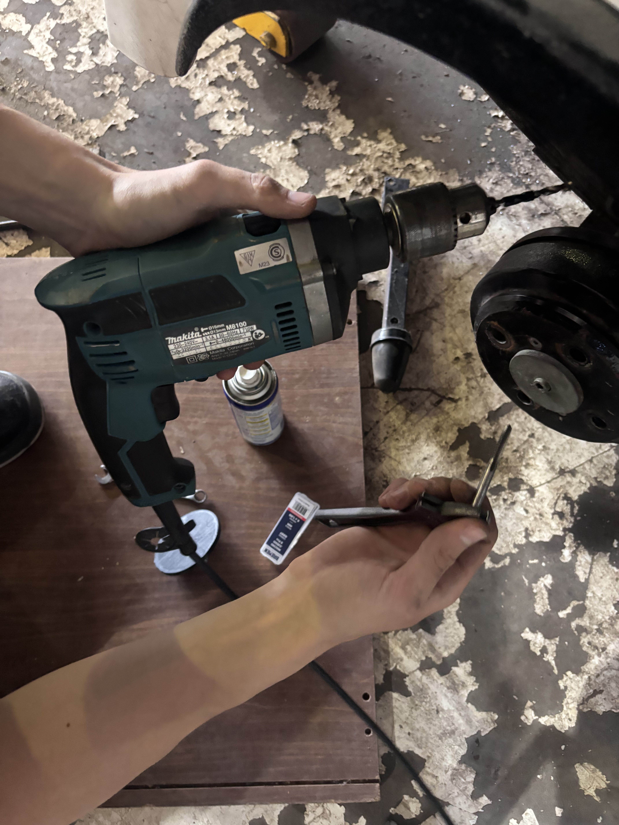
Carros Melex/Armado/Colocacion disco segmentado/Colocacion disco segmentado2.JPG
